Alemagpie/Teensy-based-Multieffect-Pedal/src/effect_chorus.cpp

/* Audio Library for Teensy 3.X
 * Copyright (c) 2014, Pete (El Supremo)
 *
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
 * THE SOFTWARE IS PROVIDED "AS IS", WITHOUT WARRANTY OF ANY KIND, EXPRESS OR
 * IMPLIED, INCLUDING BUT NOT LIMITED TO THE WARRANTIES OF MERCHANTABILITY,
 * FITNESS FOR A PARTICULAR PURPOSE AND NONINFRINGEMENT. IN NO EVENT SHALL THE
 * AUTHORS OR COPYRIGHT HOLDERS BE LIABLE FOR ANY CLAIM, DAMAGES OR OTHER
 * LIABILITY, WHETHER IN AN ACTION OF CONTRACT, TORT OR OTHERWISE, ARISING FROM,
 * OUT OF OR IN CONNECTION WITH THE SOFTWARE OR THE USE OR OTHER DEALINGS IN
 * THE SOFTWARE.
 */

#include <Arduino.h>
#include "effect_chorus.h"

/******************************************************************/

//                A u d i o E f f e c t C h o r u s
// Written by Pete (El Supremo) Jan 2014
// 140529 - change to handle mono stream - change modify() to voices()
// 140219 - correct storage class (not static)

boolean AudioEffectChorus::begin(short *delayline,int d_length,int n_chorus)
{
#if 0
Serial.print("AudioEffectChorus.begin(Chorus delay line length = ");
Serial.print(d_length);
Serial.print(", n_chorus = ");
Serial.print(n_chorus);
Serial.println(")");
#endif

  l_delayline = NULL;
  delay_length = 0;
  l_circ_idx = 0;

  if(delayline == NULL) {
    return(false);
  }
  if(d_length < 10) {
    return(false);
  }
  if(n_chorus < 1) {
    return(false);
  }
  
  l_delayline = delayline;
  delay_length = d_length/2;
  num_chorus = n_chorus;
 
  return(true);
}

void AudioEffectChorus::voices(int n_chorus)
{
  num_chorus = n_chorus;
}

void AudioEffectChorus::d_lenght(int lenght) {
  delay_length = lenght/2;
}

//int last_idx = 0;
void AudioEffectChorus::update(void)
{
  audio_block_t *block;
  short *bp;
  int sum;
  int c_idx;

  if(l_delayline == NULL)return;
  
  // do passthru
  // It stores the unmodified data in the delay line so that
  // it isn't as likely to click
  if(num_chorus <= 1) {
    // Just passthrough
    block = receiveWritable(0);
    if(block) {
      bp = block->data;
      for(int i = 0;i < AUDIO_BLOCK_SAMPLES;i++) {
        l_circ_idx++;
        if(l_circ_idx >= delay_length) {
          l_circ_idx = 0;
        }
        l_delayline[l_circ_idx] = *bp++;
      }
      transmit(block,0);
      release(block);
    }
    return;
  }

  //          L E F T  C H A N N E L

  block = receiveWritable(0);
  if(block) {
    bp = block->data;
    uint32_t tmp = delay_length/(num_chorus - 1) - 1;
    for(int i = 0;i < AUDIO_BLOCK_SAMPLES;i++) {
      l_circ_idx++;
      if(l_circ_idx >= delay_length) {
        l_circ_idx = 0;
      }
      l_delayline[l_circ_idx] = *bp;
      sum = 0;
      c_idx = l_circ_idx;
      for(int k = 0; k < num_chorus; k++) {
        sum += l_delayline[c_idx];
        if(num_chorus > 1)c_idx -= tmp;
        if(c_idx < 0) {
          c_idx += delay_length;
        }
      }
      *bp++ = sum/num_chorus;
    }

    // transmit the block
    transmit(block,0);
    release(block);
  }
}


void AudioEffectChorus::setParamLevel(int index, float level) {}

void AudioEffectChorus::init(float p1, float p2, float p3, float p4) {}

float getParamLevel(int index) {return 0;}

/*
//param1 = num_chorus (voices), param2 = delay_lenght (depth), param3 = param4 = null
void AudioEffectChorus::setParamLevel(int index, float level) {
  if(index < 0 || index > parameterCount - 1 || level < 0 || level > 1) {
    return;
  }

  levels[index] = level;
  int value = (int)Utility::calculateParamValue(ranges[index], level);

  switch(index) {
    case 0:
    //change num voices
    voices(value);
    break;

    case 1:
    //change delay lenght
    d_lenght(value);
    break;

    case 2: case 3: default:
    break;
  }
}


void AudioEffectChorus::init(float p1, float p2, float p3, float p4) {
  short *dl = new short;
  this->begin(dl, (int)p2, (int)p1);
}
*/

AudioEffectChorus::~AudioEffectChorus(void) {
  delete(l_delayline);
  l_delayline = nullptr;
}
