Alemagpie/Teensy-based-Multieffect-Pedal/src/Effects.cpp

#include "Effects.h"

DistortionEffect dist;
TremoloEffect trem;
BitCrusherEffect bitcrush;
VibratoEffect vib;
ChorusEffect ch;
VolumeEffect vl;
DelayEffect de;
BiquadEffect bq;
PhaserEffect ph;
EnvelopeFilterEffect envf;
SquarerEffect sqr;
RingModulatorEffect rngMd;
