Alemagpie/Teensy-based-Multieffect-Pedal/include/EffectAdapter.h

#ifndef EFFECT_ADAPTER_H
#define EFFECT_ADAPTER_H

#include <string>
#include <vector>
#include "Utility.h"
#include "CustomRange.h"
#include <initializer_list>

class EffectAdapter {
    public:
    EffectAdapter();
    EffectAdapter(std::initializer_list<CustomRange> r) : ranges(r) {};

    float getParamLevel(int index) const {return (index < 0 || index > parameterCount - 1) ? 0 : levels[index];}
    virtual void setParamLevel(int index, uint16_t level) = 0;

    /*
    //The parameter influenced by the tap tempo has to be set internally by the developer, not asssigned by the user
    virtual void setParamFromTapTempo(float tapTempo) {};
    //The parameter influenced by the expr pedal has to be asssigned by the user
    virtual void assignExprToParam(uint8_t paramIndex) {};
    //The parameter influenced by the hold press has to be set internally by the developer, not asssigned by the user
    virtual void setParamAsHold() {}; 
    */

    bool toggleEnable(){
        enabled = !enabled;
        return enabled;
    }
    virtual AudioStream* getAudioStreamComponent() = 0;

    const char* getEffectName() { return effectName; }
    const uint8_t getEffectID() { return ID; }
    std::vector<const char*>* getParamNames() { return &paramName; }

    protected:
    uint8_t ID;
    std::vector<CustomRange> ranges;
    std::vector<uint16_t> levels = {0, 0, 0, 0};
    const char* effectName;
    std::vector<const char*> paramName;
    std::vector<bool> isParamLog = {0, 0, 0, 0};
    bool enabled = false;
    static const int parameterCount = 4;
};

#endif
