Alemagpie/Teensy-based-Multieffect-Pedal/src/effects/squarer_effect.cpp

#include "effects/squarer_effect.h"

void SquarerEffect::update(void) {
    audio_block_t *block;

    block = receiveWritable();

    if(!block) {
        return;
    }


    if(enabled) {
        inputSamplePtr = block->data;
        for(int i = 0;i < AUDIO_BLOCK_SAMPLES;i++) {
            int16_t d, s1, s2, out;
            d = s1 = s2 = 0;

            //Dry sample
            d = *inputSamplePtr;

            //Same octave square wave
            if(d > threshold && isNeg) {
                isNeg = false;
                s1 = 32767;
                crossings++;
            } else if(d < -threshold && !isNeg) {
                isNeg = true;
                s1 = -32767;
                crossings++;
            }

            //Down octave square wave
            if((crossings % 2 == 0) && crossings != 0) {
                crossings = 0;
                dwnOctaveState = !dwnOctaveState;
                s2 = dwnOctaveState ? 32767 : -32767;
            }
            
            lp_m1.process(s1);
            lp_m2.process(s2);
            out = saturate16(2 * mx_m.process(d, s1, s2));  //Makeup gain of 2
            *inputSamplePtr = out;
            inputSamplePtr++;
        }
    } 

    transmit(block);
    release(block);
}

void SquarerEffect::setParamLevel(int writeIndex, uint16_t level) {
    if(writeIndex < 0 || writeIndex > parameterCount - 1) {
        return;
    }

    //update parameters levels
    levels[writeIndex] = level;

    float valueLin = Utility::calculateParamValueLin(ranges[writeIndex], (float)level/65536.0f );
    float valueLog = Utility::calculateParamValueLog(ranges[writeIndex], (float)level/65536.0f );

    switch(writeIndex) {
        case 0:
            dry = (uint8_t) valueLin;
            mx_m.setGain(0, dry);
        break;

        case 1:
            sq1 = (uint8_t) valueLin;
            mx_m.setGain(1, sq1);
        break;

        case 2: 
            sq2 = (uint8_t) valueLin;
            mx_m.setGain(2, sq2);
        break;

        case 3: 
            lp_m1.setCutoff(valueLog);
            lp_m2.setCutoff(valueLog);
        break;
        
        default:
        break;
    }
}
