Alemagpie/Teensy-based-Multieffect-Pedal/include/Utility.h

#ifndef UTILITY_H
#define UTILITY_H

#include <Arduino.h>
#include <Audio.h>
#include "CustomRange.h"
#include <dspinst.h>

constexpr int16_t TANH_MAX = 3;
constexpr int TANH_ENTRIES = 120;
constexpr int16_t INV_TANH_STEP = (TANH_ENTRIES)/TANH_MAX;
constexpr float INV_TANH_SCALE = 1.0f/32767.0f;
PROGMEM static const int16_t tanhLUT[TANH_ENTRIES] = {
    0, 819, 1636, 2452, 3265, 4074, 4878, 5676, 6467, 7250, 8025, 8790, 9545, 10289, 11022, 11742, 
    12449, 13143, 13824, 14490, 15142, 15778, 16400, 17006, 17597, 18172, 18731, 19275, 19803, 20315, 
    20811, 21292, 21758, 22208, 22644, 23064, 23470, 23862, 24240, 24604, 24955, 25292, 25617, 25929, 
    26229, 26518, 26795, 27061, 27316, 27561, 27795, 28020, 28236, 28442, 28640, 28829, 29010, 29183, 
    29349, 29507, 29658, 29803, 29942, 30074, 30200, 30320, 30435, 30545, 30650, 30750, 30846, 30937, 
    31023, 31106, 31185, 31261, 31333, 31401, 31466, 31528, 31588, 31644, 31698, 31749, 31798, 31845, 
    31889, 31931, 31972, 32010, 32046, 32081, 32114, 32146, 32176, 32204, 32232, 32257, 32282, 32306, 
    32328, 32349, 32369, 32389, 32407, 32424, 32441, 32457, 32472, 32486, 32500, 32513, 32525, 32537, 
    32548, 32559, 32569, 32578, 32587, 32596, 
};


constexpr int SIN_ENTRIES = 419;
PROGMEM static const int16_t sinLUT[SIN_ENTRIES] = {
    0, 491, 982, 1474, 1964, 2455, 2945, 3434, 3922, 4410, 4896, 5382, 5866, 6349, 6830, 7310, 
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
    static int16_t fastTanh(int16_t x);
    static int16_t fastSin(int16_t x);
    static int16_t fastExp(int16_t x);  //y = (10^x - 1) / 9
};

#endif
