Alemagpie/Teensy-based-Multieffect-Pedal/src/Utility.cpp

#include "Utility.h"

int16_t Utility::fastTanh(int16_t x) {
  bool isNeg = x < 0;
  uint16_t absValue = isNeg ? -x : x;

  uint32_t index = ((uint32_t)absValue * (TANH_ENTRIES - 1));

  // Integer part (top bits)
  uint16_t index_int  = index >> 15;
  // Fractional part (low 15 bits)
  uint16_t index_index_frac = index & 0x7FFF;

  if (index_int >= TANH_ENTRIES - 1) {
    index_int = TANH_ENTRIES - 2;
  }

  int32_t delta  = (int32_t)tanhLUT[index_int + 1] - (int32_t)tanhLUT[index_int];
  int32_t interp = (delta * index_index_frac) >> 15;
  int16_t y = tanhLUT[index_int] + interp;

  return isNeg ? -y : y;
}

int16_t Utility::fastSin(int16_t x)
{
  uint32_t idx = ((uint32_t)(uint16_t)x * (SIN_ENTRIES - 1));

  uint16_t index_int  = idx >> 15;
  uint16_t index_frac = idx & 0x7FFF;

  if (index_int >= SIN_ENTRIES - 1) {
    index_int = SIN_ENTRIES - 2;
  }

  int32_t delta = (int32_t)sinLUT[index_int + 1] - (int32_t)sinLUT[index_int];
  int32_t interp = (delta * index_frac) >> 15;

  return saturate16(sinLUT[index_int] + interp);
}

int16_t Utility::fastExp(int16_t x) {
  // Precondition: x is always non-negative (Q15-style pot value, [0, 32767])
  if (x < 0) x = 0; 

  uint32_t idx = (uint32_t)(uint16_t)x * (EXP_ENTRIES - 1);

  uint16_t index_int  = idx >> 15;
  uint16_t index_frac = idx & 0x7FFF;

  if (index_int >= EXP_ENTRIES - 1) {
      index_int = EXP_ENTRIES - 2;
  }

  int32_t delta  = (int32_t)expLUT[index_int + 1] - (int32_t)expLUT[index_int];
  int32_t interp = (delta * (int32_t)index_frac) >> 15;
  int32_t result = (int32_t)expLUT[index_int] + interp;

  return saturate16(result);
}
